jcfurey/cambridge_reverb/bom/bom.csv

# GENERATED from the schematic by kicad/gen/gen_bom.py -- do not hand-edit.
# Electrical rows are 1:1 with the KiCad netlist; mechanical/off-board items follow.
ref | description | value | footprint | digikey_pn | mouser_pn | qty | notes
C_mrb_450 | Capacitor (film/ceramic) | 120nF (opt) | C_Disc_D7.5mm_W2.5mm_P5.00mm |  |  | 1
C_mrb_600 | Capacitor (film/ceramic) | 68nF | C_Disc_D7.5mm_W2.5mm_P5.00mm |  |  | 1
C_mrb_750 | Capacitor (film/ceramic) | 47nF (opt) | C_Disc_D7.5mm_W2.5mm_P5.00mm |  |  | 1
C_mrb_in | Capacitor (film/ceramic) | 100nF | C_Disc_D7.5mm_W2.5mm_P5.00mm |  |  | 1
C_mrb_out | Capacitor (film/ceramic) | 100nF | C_Disc_D7.5mm_W2.5mm_P5.00mm |  |  | 1
L1 | MRB tank inductor (reused/off-board) | 1H toroid | Inductor_MRB_1H_Toroid |  |  | 1 | reuse original ~1H, or 2x 0.5H Fasel
R_fs_mrb | Resistor | 100k | R_Axial_DIN0207_L6.3mm_D2.5mm_P5.08mm_Vertical |  |  | 1
R_mrb_ser | Resistor | 10k | R_Axial_DIN0207_L6.3mm_D2.5mm_P5.08mm_Vertical |  |  | 1
TP_MRB_OUT | Test point (header pin or wire loop) | MRB | TestPoint_THT_D2.0mm_Label |  |  | 1 | bench test point: fit a header pin or a bare 0.6 mm wire loop; silk shows the net
C_bref | LM1875 bias-divider bypass (kills the rail-ripple path into the + input) | 100uF/25V | CP_Radial_D6.3mm_P2.50mm |  |  | 1 | 100 uF/25 V bypass on the LM1875 bias divider; without it the divider injected rail ripple x23 into the speaker (spice/ac_hum_psrr.cir)
C_byp1 | Capacitor (film/ceramic) | 100nF | C_Disc_D7.5mm_W2.5mm_P5.00mm |  |  | 1
C_byp2 | Capacitor (electrolytic) | 10uF/50V | CP_Radial_D5.0mm_P2.00mm |  |  | 1
C_fb_hf | Capacitor (film/ceramic) | 1nF | C_Disc_D7.5mm_W2.5mm_P5.00mm |  |  | 1
C_gain | Capacitor (electrolytic) | 22uF/25V | CP_Radial_D5.0mm_P2.00mm |  |  | 1
C_in_pa | Capacitor (film/ceramic) | 1uF | C_Disc_D7.5mm_W2.5mm_P5.00mm |  |  | 1
C_out | Capacitor (electrolytic) | 2200uF/35V | CP_Radial_D16.0mm_P7.50mm |  |  | 1 | REQUIRED for single-supply (errata #7)
C_zobel | Capacitor (film/ceramic) | 100nF | C_Disc_D7.5mm_W2.5mm_P5.00mm |  |  | 1
D1 | Diode | 1N4007 | D_DO-41_SOD81_P10.16mm_Horizontal | 1N4007-E3/54GICT-ND | 625-1N4007-E3 | 1 | output clamp
D2 | Diode | 1N4007 | D_DO-41_SOD81_P10.16mm_Horizontal | 1N4007-E3/54GICT-ND | 625-1N4007-E3 | 1 | output clamp
IC_PA | Power amplifier | LM1875T | TO-220-5_Vertical_P1.70mm_LM1875 | LM1875T/NOPB-ND | 926-LM1875T/NOPB | 1 | Single-source (TI) - buy a spare. Heatsink <=2.5 C/W + mica; NOT socketed
R_bias1 | Resistor | 22k | R_Axial_DIN0207_L6.3mm_D2.5mm_P5.08mm_Vertical |  |  | 1
R_bias2 | Resistor | 22k | R_Axial_DIN0207_L6.3mm_D2.5mm_P5.08mm_Vertical |  |  | 1
R_bias3 | LM1875 + input bias feed (from the bypassed divider) | 22k | R_Axial_DIN0207_L6.3mm_D2.5mm_P5.08mm_Vertical |  |  | 1
R_fb | Resistor | 22k | R_Axial_DIN0207_L6.3mm_D2.5mm_P5.08mm_Vertical |  |  | 1
R_gain | Resistor | 1k | R_Axial_DIN0207_L6.3mm_D2.5mm_P5.08mm_Vertical |  |  | 1
R_zobel | Resistor | 10R | R_Axial_DIN0207_L6.3mm_D2.5mm_P5.08mm_Vertical |  |  | 1
TP_GND_PA | Test point (header pin or wire loop) | GND | TestPoint_THT_D2.0mm_Label |  |  | 1 | bench test point: fit a header pin or a bare 0.6 mm wire loop; silk shows the net
TP_PA_BIAS | Test point (header pin or wire loop) | PA_B | TestPoint_THT_D2.0mm_Label |  |  | 1 | bench test point: fit a header pin or a bare 0.6 mm wire loop; silk shows the net
TP_PA_OUT | Test point (header pin or wire loop) | PA_OUT | TestPoint_THT_D2.0mm_Label |  |  | 1 | bench test point: fit a header pin or a bare 0.6 mm wire loop; silk shows the net
TP_SPK | Test point (header pin or wire loop) | SPK | TestPoint_THT_D2.0mm_Label |  |  | 1 | bench test point: fit a header pin or a bare 0.6 mm wire loop; silk shows the net
BR1 | Bridge rectifier | KBP410G | Bridge_KBP_P3.81mm | KBP410G-ND | 821-KBP410G | 1 | Or 4x 1N4007
C101 | Capacitor (film/ceramic) | 10nF/100V | C_Disc_D7.5mm_W2.5mm_P5.00mm |  | 594-K104Z15Y5VF5TL2 | 1 | bridge snubber
C102 | Capacitor (film/ceramic) | 10nF/100V | C_Disc_D7.5mm_W2.5mm_P5.00mm |  | 594-K104Z15Y5VF5TL2 | 1 | bridge snubber
C103 | Capacitor (film/ceramic) | 10nF/100V | C_Disc_D7.5mm_W2.5mm_P5.00mm |  | 594-K104Z15Y5VF5TL2 | 1 | bridge snubber
C104 | Capacitor (film/ceramic) | 10nF/100V | C_Disc_D7.5mm_W2.5mm_P5.00mm |  | 594-K104Z15Y5VF5TL2 | 1 | bridge snubber
C_adj | LM317 ADJ bypass: +15 dB ripple rejection, ~10x less rail noise | 10uF/25V | CP_Radial_D5.0mm_P2.00mm |  |  | 1 | 10 uF/25 V on the LM317 ADJ pin (TI: 65 -> 80 dB ripple rejection; output noise falls ~10x) -- spice/noise_frontend.cir
C_filt1 | Capacitor (electrolytic) | 1000uF/50V | CP_Radial_D12.5mm_P5.00mm |  | 667-EEU-FC1H102 | 1 | low-ESR pre-filter bulk
C_filt2 | Capacitor (electrolytic) | 1000uF/50V | CP_Radial_D12.5mm_P5.00mm |  | 667-EEU-FC1H102 | 1 | low-ESR pre-filter bulk
C_main | Capacitor (electrolytic) | 4700uF/50V | CP_Radial_D18.0mm_P7.50mm |  | 667-EEU-FC1H472 | 1 | low-ESR; or 2x2200uF if PCB-mounted (errata #16)
C_pre | Preamp rail decoupling (with R_pre) | 220uF/25V | CP_Radial_D6.3mm_P2.50mm |  |  | 1 | 220 uF/25 V; with R_pre 100R a 7 Hz corner on the preamp/recovery JFET rail -- the resistor-loaded JFET stages have ~0 dB PSRR
C_reg_in | Capacitor (electrolytic) | 10uF/50V | CP_Radial_D5.0mm_P2.50mm |  | 581-TAP106K050SCS | 1 | tantalum
C_reg_out1 | Capacitor (electrolytic) | 10uF/25V | CP_Radial_D5.0mm_P2.50mm |  | 581-TAP106K025SCS | 1 | tantalum
C_reg_out2 | Capacitor (film/ceramic) | 100nF | C_Disc_D7.5mm_W2.5mm_P5.00mm |  |  | 1
C_vbr | Capacitor (electrolytic) | 47uF/25V | CP_Radial_D6.3mm_P2.50mm |  |  | 1
C_vbt | Capacitor (electrolytic) | 47uF/25V | CP_Radial_D6.3mm_P2.50mm |  |  | 1
F1 | Fuse | 1A SB | Fuseholder_Clip-5x20mm_Eaton_1A5601-01_Inline_P20.80x6.76mm_D1.70mm_Horizontal |  | 576-0273001.H | 1 | secondary fuse; prefer AC-secondary placement (roast R5)
R_27V | Resistor | 100R/1W | R_Axial_DIN0414_L11.9mm_D4.5mm_P15.24mm_Horizontal |  |  | 1 | LM317-input RC pre-filter w/ C_filt1 (VREG_IN ~32V, roast R2)
R_bleed | Resistor | 10k/5W | R_Axial_Power_L20.0mm_W6.4mm_P25.40mm |  |  | 1
R_pre | Preamp rail decoupling (with C_pre) | 100R | R_Axial_DIN0207_L6.3mm_D2.5mm_P5.08mm_Vertical |  |  | 1
R_reg1 | Resistor | 240R | R_Axial_DIN0207_L6.3mm_D2.5mm_P5.08mm_Vertical |  | 603-MFR-25FBF52-240R | 1
R_reg2 | Resistor | 3.09k | R_Axial_DIN0207_L6.3mm_D2.5mm_P5.08mm_Vertical |  |  | 1 | 3.09k E96 -> 17.34V (errata #10)
R_vbr1 | Resistor | 100k | R_Axial_DIN0207_L6.3mm_D2.5mm_P5.08mm_Vertical |  |  | 1
R_vbr2 | Resistor | 100k | R_Axial_DIN0207_L6.3mm_D2.5mm_P5.08mm_Vertical |  |  | 1
R_vbt1 | Resistor | 100k | R_Axial_DIN0207_L6.3mm_D2.5mm_P5.08mm_Vertical |  |  | 1
R_vbt2 | Resistor | 100k | R_Axial_DIN0207_L6.3mm_D2.5mm_P5.08mm_Vertical |  |  | 1
T1 | Power transformer (reused/off-board) | reuse / AnTek AS-0524 | WirePad_1x03_P5.08mm_D1.5mm |  |  | 1 | reuse original (test ~48VAC) or AnTek AS-0524 50VA
TP_17V | Test point (header pin or wire loop) | +17V | TestPoint_THT_D2.0mm_Label |  |  | 1 | bench test point: fit a header pin or a bare 0.6 mm wire loop; silk shows the net
TP_33V5 | Test point (header pin or wire loop) | +33V5 | TestPoint_THT_D2.0mm_Label |  |  | 1 | bench test point: fit a header pin or a bare 0.6 mm wire loop; silk shows the net
TP_GND_PSU | Test point (header pin or wire loop) | GND | TestPoint_THT_D2.0mm_Label |  |  | 1 | bench test point: fit a header pin or a bare 0.6 mm wire loop; silk shows the net
TP_VRAW | Test point (header pin or wire loop) | VRAW | TestPoint_THT_D2.0mm_Label |  |  | 1 | bench test point: fit a header pin or a bare 0.6 mm wire loop; silk shows the net
TP_VREG_IN | Test point (header pin or wire loop) | VREG | TestPoint_THT_D2.0mm_Label |  |  | 1 | bench test point: fit a header pin or a bare 0.6 mm wire loop; silk shows the net
U1 | +17V rail regulator | LM317T | TO-220-3_Vertical | LM317T/NOPB-ND | 926-LM317T/NOPB | 1
C_cpl12 | Capacitor (film/ceramic) | 100nF | C_Disc_D7.5mm_W2.5mm_P5.00mm |  |  | 1
C_cpl_out | Capacitor (film/ceramic) | 1uF | C_Disc_D7.5mm_W2.5mm_P5.00mm |  |  | 1
C_in_pre | Capacitor (film/ceramic) | 47nF | C_Disc_D7.5mm_W2.5mm_P5.00mm |  |  | 1
C_pres | Capacitor (film/ceramic) | 100pF | C_Disc_D7.5mm_W2.5mm_P5.00mm |  |  | 1
C_s1 | Capacitor (electrolytic) | 10uF/25V | CP_Radial_D5.0mm_P2.00mm |  |  | 1
C_s2 | Capacitor (electrolytic) | 10uF/25V | CP_Radial_D5.0mm_P2.00mm |  |  | 1
Q1 | Preamp JFET | MMBF5457 | TO-92_Inline_Wide | MMBF5457CT-ND | 863-MMBF5457 | 1 | AVAILABILITY WATCH (JFETs going EOL) - buy spares; alts J113/LSK170. THT board: SOT-23 on a TO-92 adapter or J113 -- pads 1/2/3 = D/S/G (errata #18); SMD variant fits it directly
Q2 | Preamp JFET | MMBF5457 | TO-92_Inline_Wide | MMBF5457CT-ND | 863-MMBF5457 | 1 | see Q1
R_d1 | Resistor | 10k | R_Axial_DIN0207_L6.3mm_D2.5mm_P5.08mm_Vertical |  |  | 1
R_d2 | Resistor | 10k | R_Axial_DIN0207_L6.3mm_D2.5mm_P5.08mm_Vertical |  |  | 1
R_g1 | Resistor | 1M | R_Axial_DIN0207_L6.3mm_D2.5mm_P5.08mm_Vertical |  |  | 1
R_g2 | Resistor | 1M | R_Axial_DIN0207_L6.3mm_D2.5mm_P5.08mm_Vertical |  |  | 1
R_s1 | Resistor | 2.2k | R_Axial_DIN0207_L6.3mm_D2.5mm_P5.08mm_Vertical |  |  | 1 | 2K2 biases Vd~12V; ~1-1.2k -> 8-9V target (errata #15), trim per device
R_s2 | Resistor | 2.2k | R_Axial_DIN0207_L6.3mm_D2.5mm_P5.08mm_Vertical |  |  | 1 | see R_s1 (errata #15)
TP_GND_PRE | Test point (header pin or wire loop) | GND | TestPoint_THT_D2.0mm_Label |  |  | 1 | bench test point: fit a header pin or a bare 0.6 mm wire loop; silk shows the net
TP_PRE_OUT | Test point (header pin or wire loop) | PRE | TestPoint_THT_D2.0mm_Label |  |  | 1 | bench test point: fit a header pin or a bare 0.6 mm wire loop; silk shows the net
TP_Q1D | Test point (header pin or wire loop) | Q1D | TestPoint_THT_D2.0mm_Label |  |  | 1 | bench test point: fit a header pin or a bare 0.6 mm wire loop; silk shows the net
TP_Q2D | Test point (header pin or wire loop) | Q2D | TestPoint_THT_D2.0mm_Label |  |  | 1 | bench test point: fit a header pin or a bare 0.6 mm wire loop; silk shows the net
C_drvin | Capacitor (film/ceramic) | 100nF | C_Disc_D7.5mm_W2.5mm_P5.00mm |  |  | 1
C_drymix | Capacitor (film/ceramic) | 1uF | C_Disc_D7.5mm_W2.5mm_P5.00mm |  |  | 1
C_rec_byp | Capacitor (electrolytic) | 10uF | CP_Radial_D5.0mm_P2.00mm |  |  | 1
C_rev1 | Capacitor (electrolytic) | 1uF | CP_Radial_D5.0mm_P2.00mm |  |  | 1
C_rev2 | Capacitor (film/ceramic) | 10nF | C_Disc_D7.5mm_W2.5mm_P5.00mm |  |  | 1
C_rev4 | Capacitor (film/ceramic) | 100nF | C_Disc_D7.5mm_W2.5mm_P5.00mm |  |  | 1
C_wetmix | Capacitor (film/ceramic) | 1uF | C_Disc_D7.5mm_W2.5mm_P5.00mm |  |  | 1
IC1 | Dual op-amp: reverb tank driver + wet/dry summer | TL072CP | DIP-8_W7.62mm | 296-1775-5-ND | 595-TL072CP | 1 | DIP-8; use a machined-pin SOCKET_IC
POT_REV | Reverb level (reused/off-board) | reuse | WirePad_1x03_P2.54mm_D1.2mm |  |  | 1
Q_rec | Reverb-recovery JFET | MMBF5457 | TO-92_Inline_Wide | MMBF5457CT-ND | 863-MMBF5457 | 1 | see Q1
REV1 | Reverb pan (high-Z input) (reused/off-board) | 4FB2A1C | WirePad_1x04_P2.54mm_D1.2mm |  |  | 1 | Accutronics/Belton 4FB2A1C ~1475ohm - NOT 4AB3C1B (8ohm)
R_drv1 | Resistor | 100k | R_Axial_DIN0207_L6.3mm_D2.5mm_P5.08mm_Vertical |  |  | 1
R_drv2 | Resistor | 10k | R_Axial_DIN0207_L6.3mm_D2.5mm_P5.08mm_Vertical |  |  | 1
R_drv3 | Resistor | 10R | R_Axial_DIN0207_L6.3mm_D2.5mm_P5.08mm_Vertical |  |  | 1
R_drvbias | Resistor | 220k | R_Axial_DIN0207_L6.3mm_D2.5mm_P5.08mm_Vertical |  |  | 1
R_drymix | Resistor | 100k | R_Axial_DIN0207_L6.3mm_D2.5mm_P5.08mm_Vertical |  |  | 1
R_fs_rev | Resistor | 100k | R_Axial_DIN0207_L6.3mm_D2.5mm_P5.08mm_Vertical |  |  | 1
R_mixfb | Resistor | 100k | R_Axial_DIN0207_L6.3mm_D2.5mm_P5.08mm_Vertical |  |  | 1
R_rec1 | Resistor | 10k | R_Axial_DIN0207_L6.3mm_D2.5mm_P5.08mm_Vertical |  |  | 1
R_rec2 | Resistor | 2.2k | R_Axial_DIN0207_L6.3mm_D2.5mm_P5.08mm_Vertical |  |  | 1
R_rec_bias | Resistor | 1M | R_Axial_DIN0207_L6.3mm_D2.5mm_P5.08mm_Vertical |  |  | 1
R_wetmix | Resistor | 100k | R_Axial_DIN0207_L6.3mm_D2.5mm_P5.08mm_Vertical |  |  | 1
TP_BLEND | Test point (header pin or wire loop) | BLEND | TestPoint_THT_D2.0mm_Label |  |  | 1 | bench test point: fit a header pin or a bare 0.6 mm wire loop; silk shows the net
TP_GND_REV | Test point (header pin or wire loop) | GND | TestPoint_THT_D2.0mm_Label |  |  | 1 | bench test point: fit a header pin or a bare 0.6 mm wire loop; silk shows the net
TP_QRD | Test point (header pin or wire loop) | QRD | TestPoint_THT_D2.0mm_Label |  |  | 1 | bench test point: fit a header pin or a bare 0.6 mm wire loop; silk shows the net
TP_TANK_IN | Test point (header pin or wire loop) | TK_IN | TestPoint_THT_D2.0mm_Label |  |  | 1 | bench test point: fit a header pin or a bare 0.6 mm wire loop; silk shows the net
TP_TANK_OUT | Test point (header pin or wire loop) | TK_OUT | TestPoint_THT_D2.0mm_Label |  |  | 1 | bench test point: fit a header pin or a bare 0.6 mm wire loop; silk shows the net
TP_VBIAS_R | Test point (header pin or wire loop) | VB_R | TestPoint_THT_D2.0mm_Label |  |  | 1 | bench test point: fit a header pin or a bare 0.6 mm wire loop; silk shows the net
FS1 | Footswitch DIN connector (reused/off-board) | DIN-6 | WirePad_1x06_P2.54mm_D1.2mm |  |  | 1
J_IN1 | 1/4in jack (panel, reused) | Input 1 | WirePad_1x02_P2.54mm_D1.2mm |  |  | 1
J_IN2 | 1/4in jack (panel, reused) | Input 2 | WirePad_1x02_P2.54mm_D1.2mm |  |  | 1
J_IN3 | 1/4in jack (panel, reused) | IN3 / FX return | WirePad_1x02_P2.54mm_D1.2mm |  |  | 1
LS1 | 10in speaker (reused/off-board) | 10in Bulldog | WirePad_1x02_P5.08mm_D1.5mm |  |  | 1
R_spk_rtn | Resistor | 0R | R_Axial_DIN0414_L11.9mm_D4.5mm_P15.24mm_Horizontal |  |  | 1
C_byp3 | Capacitor (film/ceramic) | 100nF | C_Disc_D7.5mm_W2.5mm_P5.00mm |  |  | 1
C_gg | Capacitor (film/ceramic) | 2.2nF | C_Disc_D7.5mm_W2.5mm_P5.00mm |  |  | 1
C_j1 | Capacitor (film/ceramic) | 22nF | C_Disc_D7.5mm_W2.5mm_P5.00mm |  |  | 1
C_j2 | Capacitor (film/ceramic) | 22nF | C_Disc_D7.5mm_W2.5mm_P5.00mm |  |  | 1
C_j3 | Capacitor (film/ceramic) | 2.2nF | C_Disc_D7.5mm_W2.5mm_P5.00mm |  |  | 1
C_j4 | Capacitor (film/ceramic) | 2.2nF | C_Disc_D7.5mm_W2.5mm_P5.00mm |  |  | 1
C_res | Capacitor (film/ceramic) | 22nF | C_Disc_D7.5mm_W2.5mm_P5.00mm |  |  | 1
C_tout | Capacitor (film/ceramic) | 1uF | C_Disc_D7.5mm_W2.5mm_P5.00mm |  |  | 1
C_treble | Capacitor (film/ceramic) | 470pF | C_Disc_D7.5mm_W2.5mm_P5.00mm |  |  | 1
C_vb3 | Capacitor (electrolytic) | 47uF/25V | CP_Radial_D6.3mm_P2.50mm |  |  | 1
IC3 | Quad op-amp: tone input buffer + x2 make-up after the passive James bass/treble network + mid-cut gyrator + output buffer | TL074CN | DIP-14_W7.62mm |  | 595-TL074CN | 1 | DIP-14; machined-pin SOCKET_IC14. Tone stack (errata #20)
POT_BASS | Bass (reused/off-board) | 250k lin | WirePad_1x03_P2.54mm_D1.2mm |  |  | 1 | reused panel pot; James network scaled for 250k lin -- if the original measures differently, scale R_j1/R_j2/R_j3 and C_j1/C_j2 to keep the same corner frequencies
POT_TREB | Treble (reused/off-board) | 250k lin | WirePad_1x03_P2.54mm_D1.2mm |  |  | 1 | reused panel pot; James network scaled for 250k lin -- scale C_j3/C_j4 inversely to keep the treble corner
POT_VOL | Volume (reused/off-board) | 250k log | WirePad_1x03_P2.54mm_D1.2mm |  |  | 1
R_fx_pad | Resistor | 10k | R_Axial_DIN0207_L6.3mm_D2.5mm_P5.08mm_Vertical |  |  | 1
R_gL | Resistor | 4.7k | R_Axial_DIN0207_L6.3mm_D2.5mm_P5.08mm_Vertical |  |  | 1
R_gg | Resistor | 180k | R_Axial_DIN0207_L6.3mm_D2.5mm_P5.08mm_Vertical |  |  | 1
R_inb | Resistor | 1M | R_Axial_DIN0207_L6.3mm_D2.5mm_P5.08mm_Vertical |  |  | 1
R_j1 | Resistor | 10k | R_Axial_DIN0207_L6.3mm_D2.5mm_P5.08mm_Vertical |  |  | 1
R_j2 | Resistor | 10k | R_Axial_DIN0207_L6.3mm_D2.5mm_P5.08mm_Vertical |  |  | 1
R_j3 | Resistor | 68k | R_Axial_DIN0207_L6.3mm_D2.5mm_P5.08mm_Vertical |  |  | 1
R_j4 | Resistor | 1k | R_Axial_DIN0207_L6.3mm_D2.5mm_P5.08mm_Vertical |  |  | 1
R_mid | Resistor | 10k | R_Axial_DIN0207_L6.3mm_D2.5mm_P5.08mm_Vertical |  |  | 1
R_mk1 | Resistor | 10k | R_Axial_DIN0207_L6.3mm_D2.5mm_P5.08mm_Vertical |  |  | 1
R_mk2 | Resistor | 10k | R_Axial_DIN0207_L6.3mm_D2.5mm_P5.08mm_Vertical |  |  | 1
R_vb31 | Resistor | 100k | R_Axial_DIN0207_L6.3mm_D2.5mm_P5.08mm_Vertical |  |  | 1
R_vb32 | Resistor | 100k | R_Axial_DIN0207_L6.3mm_D2.5mm_P5.08mm_Vertical |  |  | 1
SW_MID | Mid-cut toggle (panel, line-reverse switch hole) | MID CUT | WirePad_1x02_P2.54mm_D1.2mm |  |  | 1 | SPST (or SPDT wired as SPST) mini toggle, panel-mount in the ORIGINAL line-reverse switch hole (no new hole); switches an audio shunt sitting at mid-rail DC -> no pop
TP_MK_OUT | Test point (header pin or wire loop) | TMK | TestPoint_THT_D2.0mm_Label |  |  | 1 | bench test point: fit a header pin or a bare 0.6 mm wire loop; silk shows the net
TP_TONE_OUT | Test point (header pin or wire loop) | TONE | TestPoint_THT_D2.0mm_Label |  |  | 1 | bench test point: fit a header pin or a bare 0.6 mm wire loop; silk shows the net
TP_VBIAS_3 | Test point (header pin or wire loop) | VB_3 | TestPoint_THT_D2.0mm_Label |  |  | 1 | bench test point: fit a header pin or a bare 0.6 mm wire loop; silk shows the net
C_dc_blk | Capacitor (electrolytic) | 10uF | CP_Radial_D5.0mm_P2.00mm |  |  | 1
C_drv | LED-driver coupling (LFO -> base) | 100uF/25V | CP_Radial_D6.3mm_P2.50mm |  |  | 1 | 100 uF/25 V electrolytic, + to the depth-pot wiper (8.5 V) side; with R_b1||R_b2 sets the 0.17 Hz LFO coupling corner
C_lfo1 | Capacitor (film/ceramic) | 1uF | C_Disc_D7.5mm_W2.5mm_P5.00mm |  |  | 1
C_lfo2 | Capacitor (film/ceramic) | 1uF | C_Disc_D7.5mm_W2.5mm_P5.00mm |  |  | 1
C_obuf_in | Capacitor (film/ceramic) | 1uF | C_Disc_D7.5mm_W2.5mm_P5.00mm |  |  | 1
IC2 | Dual op-amp: tremolo LFO + output buffer | TL072CP | DIP-8_W7.62mm | 296-1775-5-ND | 595-TL072CP | 1 | DIP-8; use a machined-pin SOCKET_IC
LED_lim | LFO limiter LED (other half-cycle) | 3mm red | LED_D3.0mm | 160-1127-ND |  | 1 | 3 mm red; the other half of the limiter (lights on the negative half-cycle)
LED_rate | LFO limiter LED = rate indicator (on-board) | 3mm red | LED_D3.0mm | 160-1127-ND |  | 1 | 3 mm red; antiparallel with LED_lim across R_lfo_fb1 = the LFO amplitude limiter (~1.6 V knee -> ~2 V LFO swing) AND the rate indicator; on-board, not panel
POT_DPT | Tremolo depth (reused/off-board) | 100k lin | WirePad_1x03_P2.54mm_D1.2mm |  |  | 1
POT_SPD_A | Tremolo speed -- dual-gang pot, gang A (series Wien arm) | 250k lin dual | WirePad_1x03_P2.54mm_D1.2mm |  |  | 1 | DUAL-GANG 250k linear, 1 part = gangs A+B (same panel hole as the original speed pot); errata #19
POT_SPD_B | Tremolo speed -- dual-gang pot, gang B (shunt Wien arm); ONE part with POT_SPD_A | 250k lin dual | WirePad_1x03_P2.54mm_D1.2mm |  |  | 1 | second gang of POT_SPD_A -- do not order twice
Q_trem | Tremolo LED driver (emitter follower, AC-coupled from the depth pot) | 2N3904 | TO-92_Inline_Wide | 2N3904FS-ND | 512-2N3904BU | 1 | any small NPN; SMD board: MMBT3904 on the EBC-renumbered SOT-23 footprint (1=E 2=B 3=C like the TO-92)
R_b1 | LED-driver base bias | 180k | R_Axial_DIN0207_L6.3mm_D2.5mm_P5.08mm_Vertical |  |  | 1
R_b2 | LED-driver base bias | 10k | R_Axial_DIN0207_L6.3mm_D2.5mm_P5.08mm_Vertical |  |  | 1
R_c | Vactrol LED series resistor | 100R | R_Axial_DIN0207_L6.3mm_D2.5mm_P5.08mm_Vertical |  |  | 1
R_e | LED-driver emitter resistor (sets peak LED current ~6 mA) | 470R | R_Axial_DIN0207_L6.3mm_D2.5mm_P5.08mm_Vertical |  |  | 1
R_fs_trem | Resistor | 100k | R_Axial_DIN0207_L6.3mm_D2.5mm_P5.08mm_Vertical |  |  | 1
R_lfo_fb1 | Resistor | 10k | R_Axial_DIN0207_L6.3mm_D2.5mm_P5.08mm_Vertical |  |  | 1
R_lfo_fb2 | Resistor | 4.7k | R_Axial_DIN0207_L6.3mm_D2.5mm_P5.08mm_Vertical |  |  | 1
R_lfo_ser | Resistor | 15k | R_Axial_DIN0207_L6.3mm_D2.5mm_P5.08mm_Vertical |  |  | 1
R_lfo_sh | Resistor | 15k | R_Axial_DIN0207_L6.3mm_D2.5mm_P5.08mm_Vertical |  |  | 1
R_obuf_b | Resistor | 100k | R_Axial_DIN0207_L6.3mm_D2.5mm_P5.08mm_Vertical |  |  | 1
R_trem1 | Resistor | 10k | R_Axial_DIN0207_L6.3mm_D2.5mm_P5.08mm_Vertical |  |  | 1
TP_GND_TREM | Test point (header pin or wire loop) | GND | TestPoint_THT_D2.0mm_Label |  |  | 1 | bench test point: fit a header pin or a bare 0.6 mm wire loop; silk shows the net
TP_LFO | Test point (header pin or wire loop) | LFO | TestPoint_THT_D2.0mm_Label |  |  | 1 | bench test point: fit a header pin or a bare 0.6 mm wire loop; silk shows the net
TP_PA_IN | Test point (header pin or wire loop) | PA_IN | TestPoint_THT_D2.0mm_Label |  |  | 1 | bench test point: fit a header pin or a bare 0.6 mm wire loop; silk shows the net
TP_TREM_OUT | Test point (header pin or wire loop) | TREM | TestPoint_THT_D2.0mm_Label |  |  | 1 | bench test point: fit a header pin or a bare 0.6 mm wire loop; silk shows the net
TP_VBIAS_T | Test point (header pin or wire loop) | VB_T | TestPoint_THT_D2.0mm_Label |  |  | 1 | bench test point: fit a header pin or a bare 0.6 mm wire loop; silk shows the net
VTL1 | Tremolo optocoupler | VTL5C1 | VTL5C1 |  |  | 1 | Xvive VTL5C1 (single-source) or DIY LED+LDR
# --- off-board / mechanical (not in netlist) ---
F_MAINS | MAINS PRIMARY fuse (SAFETY) | T800mA 250V slow-blow | 5x20mm |  |  | 1 | IEC inlet primary fuse (120V; ~T400mA@230V). REQUIRED, was missing (roast R1). Off-board
F_MAINS_holder | Fused IEC inlet / panel fuse holder |  | panel |  |  | 1 | carries the mains fuse
F1_holder | Secondary fuse holder | 5x20mm | PCB/panel |  | 534-3557 | 1
SOCKET_IC | 8-pin DIP machined-pin socket | turned-pin | DIP-8 | ED3008-5-ND | 575-193308 | 2 | REQUIRED for IC1/IC2 (machined, not stamped)
SOCKET_IC14 | 14-pin DIP machined-pin socket | turned-pin | DIP-14 |  |  | 1 | REQUIRED for IC3 (tone stack TL074)
SOCKET_U1 | TO-220 socket (optional) | 3-pin | TO-220 |  |  | 0 | optional LM317 field-swap; LM1875 stays soldered
HS_LM1875 | Heatsink for LM1875 | <=2.5 C/W | bracket |  |  | 1 | reuse original bracket; mica + shoulder washer
INS_MICA | TO-220 mica insulator + bushing |  |  |  |  | 1 | for LM1875
STANDOFF | Nylon standoffs + screws |  |  |  |  | 4 | PCB mounting
